WingTangWong/ESP8266_Programming_D1_Mini_Pogo_Jig/EAGLE/ESP12_Harness.sch

## EAGLE design EAGLE/ESP12_Harness.sch (2017-02-26)


Parts:
_: ESP12
__: ESP12

Connections:
GND: _.GND, __.GND
unnamed: _.GPIO13, __.GPIO13
unnamed: _.GPIO12, __.GPIO12
unnamed: _.GPIO14, __.GPIO14
unnamed: _.GPIO16, __.GPIO16
unnamed: _.CH_PD, __.CH_PD
unnamed: _.ADC, __.ADC
unnamed: _.RESET, __.RESET
unnamed: _.GPIO15, __.GPIO15
unnamed: _.GPIO2, __.GPIO2
unnamed: _.GPIO0, __.GPIO0
unnamed: _.GPIO5, __.GPIO5
unnamed: _.GPIO4, __.GPIO4
unnamed: _.RX, __.RX
unnamed: _.TX, __.TX
VCC: _.VCC, __.VCC
