WingTangWong/ESP8266_Programming_D1_Mini_Pogo_Jig/KICAD/ESP12_Harness.kicad_sch

## KiCad design KICAD/ESP12_Harness.kicad_sch (2022-07-24)


Parts:
POGO-ESP-12: ESP12
WEMOS-D1: ESP12

Connections:
unnamed: POGO-ESP-12.ADC, WEMOS-D1.ADC
unnamed: POGO-ESP-12.CH_PD, WEMOS-D1.CH_PD
unnamed: POGO-ESP-12.GND, WEMOS-D1.GND
unnamed: POGO-ESP-12.GPIO0, WEMOS-D1.GPIO0
unnamed: POGO-ESP-12.GPIO2, WEMOS-D1.GPIO2
unnamed: POGO-ESP-12.GPIO4, WEMOS-D1.GPIO4
unnamed: POGO-ESP-12.GPIO5, WEMOS-D1.GPIO5
unnamed: POGO-ESP-12.GPIO12, WEMOS-D1.GPIO12
unnamed: POGO-ESP-12.GPIO13, WEMOS-D1.GPIO13
unnamed: POGO-ESP-12.GPIO14, WEMOS-D1.GPIO14
unnamed: POGO-ESP-12.GPIO15, WEMOS-D1.GPIO15
unnamed: POGO-ESP-12.GPIO16, WEMOS-D1.GPIO16
unnamed: POGO-ESP-12.RESET, WEMOS-D1.RESET
unnamed: POGO-ESP-12.RX, WEMOS-D1.RX
unnamed: POGO-ESP-12.TX, WEMOS-D1.TX
unnamed: POGO-ESP-12.VCC, WEMOS-D1.VCC
